mszczuj/jugglo/python/server.py

import socket

HOST = '0.0.0.0'
PORT = 50555

def main():
    with socket.socket(socket.AF_INET, socket.SOCK_STREAM) as s:
        s.setsockopt(socket.SOL_SOCKET, socket.SO_REUSEADDR, 1)
        s.bind((HOST, PORT))
        s.listen()
        print(f"Server listening on {HOST}:{PORT}")
        
        while True:
            conn, addr = s.accept()
            with conn:
                print(f"Connected by {addr}")
                while True:
                    data = conn.recv(1024)
                    if not data:
                        break
                    print(f"Received: {data.decode('utf-8', errors='ignore')}")

if __name__ == "__main__":
    main()
